Sacamoto84/ESP32_C3_Uart_to_Udp/src/network/refreshTcpClientConnectionState.cpp

#include "network_internal.h"

// Обновляет кэшированное состояние потокового клиента без опоры на короткое замыкание bool().
bool refreshTcpClientConnectionState(const char *disconnectReason)
{
    if (tcpClient.connected())
    {
        tcpClientConnected = true;
        return true;
    }

    if (tcpClientConnected)
    {
        disconnectTcpClient(disconnectReason);
    }

    return false;
}
