Sacamoto84/ESP32_C3_Uart_to_Udp/src/network/initWiFi.cpp

#include "network_internal.h"
#include "status_led.h"

namespace
{
// Загружает и проверяет сохранённые поля static IP перед запуском Wi-Fi.
bool loadStaticIpConfig(IPAddress &localIp, IPAddress &gateway, IPAddress &subnet)
{
    String localIpString = db.get(kk::staticIp);
    String gatewayString = db.get(kk::staticGateway);
    String subnetString = db.get(kk::staticSubnet);

    const bool ok = localIp.fromString(localIpString) &&
                    gateway.fromString(gatewayString) &&
                    subnet.fromString(subnetString);

    if (!ok)
    {
        projectLog.println("Static IP enabled, but one of the IP fields is invalid. Falling back to DHCP");
    }

    return ok;
}

#if PROJECT_HAS_SCREEN
#if SCREEN_WIDTH == 72 && SCREEN_HEIGHT == 40
constexpr const uint8_t *kStartupDisplayFont = u8g2_font_4x6_tf;
constexpr uint8_t kStartupSubtitleY = 8;
constexpr uint8_t kStartupProgressY = 16;
constexpr uint8_t kStartupMessageY = 24;
#else
constexpr const uint8_t *kStartupDisplayFont = u8g2_font_7x13_tr;
constexpr uint8_t kStartupSubtitleY = 12;
constexpr uint8_t kStartupProgressY = 24;
constexpr uint8_t kStartupMessageY = 36;
#endif

// Сбрасывает стартовый экран в единое текстовое состояние рисования.
void beginStartupScreenFrame()
{
    display.clearBuffer();
    display.setDrawColor(1);
    display.setFontMode(1);
    display.setFont(kStartupDisplayFont);
    display.setFontPosTop();
}

// Рисует простую индикацию прогресса в виде точек.
void drawDotProgress(uint8_t y, int count)
{
    if (count <= 0)
    {
        return;
    }

    display.setCursor(0, y);
    for (int i = 0; i < count && i < 20; ++i)
    {
        display.print('.');
    }
}

// Рисует один кадр стартового/прогресс-экрана во время подключения Wi-Fi.
void renderWiFiStartupScreen(const char *title, const char *subtitle, int dots, const char *message)
{
    beginStartupScreenFrame();

    if (title != nullptr && title[0] != '\0')
    {
        display.setCursor(0, 0);
        display.print(title);
    }

    if (subtitle != nullptr && subtitle[0] != '\0')
    {
        display.setCursor(0, kStartupSubtitleY);
        display.print(subtitle);
    }

    drawDotProgress(kStartupProgressY, dots);

    if (message != nullptr && message[0] != '\0')
    {
        display.setCursor(0, kStartupMessageY);
        display.print(message);
    }

    drawStartupVersionFooter();
    display.sendBuffer();
}
#endif
}

// Подключается к Wi-Fi по сохранённым настройкам и при необходимости уходит в AP-режим.
void initWiFi()
{
    int count = 0;
    bool needAP = false;

    // Перед стартом Wi-Fi опускаем частоту CPU, чтобы уменьшить пик потребления.
    setCpuFrequencyMhz(80);

    WiFi.mode(WIFI_STA);

    if (db.get(kk::useStaticIp))
    {
        IPAddress localIp;
        IPAddress gateway;
        IPAddress subnet;

        if (loadStaticIpConfig(localIp, gateway, subnet))
        {
            if (WiFi.config(localIp, gateway, subnet))
            {
                projectLog.print("Static IP enabled: ");
                projectLog.print(localIp);
                projectLog.print(" gateway ");
                projectLog.print(gateway);
                projectLog.print(" subnet ");
                projectLog.println(subnet);
            }
            else
            {
                projectLog.println("WiFi.config failed, falling back to DHCP");
            }
        }
    }

    // Мощность берём из настроек; позже можем понизить её до 8.5 dBm при ретрае.
    // Старые/повреждённые значения не позволяем применить выше 19.5 dBm.
    const int savedPower = db.get(kk::wifiPower);
    const int requestedPower = sanitizeConfiguredWifiTxPower(savedPower);
    if (requestedPower != savedPower)
    {
        projectLog.printf("WiFi TX power: saved value %d is unsupported, reset to %d\n",
                      savedPower,
                      requestedPower);
        db.set(kk::wifiPower, requestedPower);
        db.update();
    }

    const bool txPowerApplied = WiFi.setTxPower((wifi_power_t)requestedPower);
    const int actualPower = WiFi.getTxPower();
    projectLog.printf("WiFi TX power: saved=%d requested=%d actual=%d (%s), apply=%s\n",
                  savedPower,
                  requestedPower,
                  actualPower,
                  WifiCurrentPowerString(actualPower).c_str(),
                  txPowerApplied ? "ok" : "failed");
    WiFi.begin(db.get(kk::WIFI_SSID), db.get(kk::WIFI_PASS));
    sendStatusLedCommand(StatusLedCommand::ConnectingToStation);

#if PROJECT_HAS_SCREEN
    {
        const String powerLabel = WifiCurrentPowerString(WiFi.getTxPower());
        renderWiFiStartupScreen("Connecting", powerLabel.c_str(), 0, nullptr);
    }
#endif

    while (WiFi.status() != WL_CONNECTED)
    {
#if PROJECT_HAS_SCREEN
        {
            const String powerLabel = WifiCurrentPowerString(WiFi.getTxPower());
            renderWiFiStartupScreen("Connecting", powerLabel.c_str(), count + 1, nullptr);
        }
#endif
        projectLog.print(db.get(kk::wifiPower));
        projectLog.print(".");
        delay(500);
        count++;

        if (count <= 20)
        {
            continue;
        }

#if PROJECT_HAS_SCREEN
        renderWiFiStartupScreen("Connecting", "8.5 dBm", 0, "Retry power");
#endif
        projectLog.println("\nWifi STA not found");
        projectLog.println("Lowering power to 8.5dBm");

        WiFi.setTxPower(WIFI_POWER_8_5dBm);
        WiFi.begin(db.get(kk::WIFI_SSID), db.get(kk::WIFI_PASS));
        count = 0;

        while (WiFi.status() != WL_CONNECTED)
        {
#if PROJECT_HAS_SCREEN
            renderWiFiStartupScreen("Connecting", "8.5 dBm", count + 1, "Retry power");
#endif
            projectLog.print(".");
            delay(500);
            count++;

            if (count <= 20)
            {
                continue;
            }

            projectLog.println("Wifi STA not found");
            needAP = true;
            break;
        }

        break;
    }

    if (needAP)
    {
#if PROJECT_HAS_SCREEN
        renderWiFiStartupScreen("Starting AP", "AP ESP32", 0, nullptr);
#endif
        projectLog.println("Starting access point");
        WiFi.mode(WIFI_AP);
        WiFi.softAP("AP ESP32");
        sendStatusLedCommand(StatusLedCommand::AccessPoint);

        if (AP_MODE_PIN >= 0 && AP_MODE_PIN != STATUS_LED_BOARD_PIN)
        {
            pinMode(AP_MODE_PIN, OUTPUT);
            digitalWrite(AP_MODE_PIN, LOW);
        }
    }
    else
    {
        sendStatusLedCommand(StatusLedCommand::WaitingForClient);
    }

#if PROJECT_HAS_SCREEN
    {
        const String connectedHost = (needAP ? WiFi.softAPIP() : WiFi.localIP()).toString();
        renderWiFiStartupScreen("Connected", connectedHost.c_str(), 0, nullptr);
    }
#endif

    projectLog.println();
    projectLog.print("Connected: ");
    projectLog.println(needAP ? WiFi.softAPIP() : WiFi.localIP());
}
