Sacamoto84/ESP32_C3_Uart_to_Udp/src/settings_portal.cpp

#include "settings_portal.h"

#include "app_globals.h"
#include "display.h"
#include "hardware.h"
#include "network_bridge.h"
#include "status_led.h"

#include <esp_wifi.h>
#include <lwip/inet.h>

namespace
{
    // Полностью перестраивает интерфейс SettingsGyver для текущего запроса.
    void buildSettingsPage(sets::Builder &b);

    // Набор кнопок выбора фиксированной мощности Wi-Fi.
    struct WifiPowerOption
    {
        int dbValue;
        const char *label;
    };

    constexpr WifiPowerOption kWifiPowerOptions[] = {
        {-4, "-1dbm (-4)"},
        {8, "2dBm (8)"},
        {34, "8.5dBm (34)"},
        {44, "11dBm (44)"},
        {52, "13dBm (52)"},
        {60, "15dBm (60)"},
        {68, "17dBm (68)"},
        {76, "19dBm (76)"},
        {78, "19.5dBm (78)"},
    };

    // Рисует одну кнопку мощности Wi-Fi и сохраняет пресет для следующего старта.
    void addWifiPowerButton(sets::Builder &b, size_t id, const WifiPowerOption &option, int currentPower)
    {
        const uint32_t color = (currentPower != option.dbValue) ? 0x808080 : 0xd55f30;
        if (b.Button(id, option.label, color))
        {
            // init с int одновременно исправляет старую запись, которая могла
            // быть сохранена как enum и при чтении давать 0.
            db.init(kk::wifiPower, option.dbValue);
            db.set(kk::wifiPower, option.dbValue);
            db.update();

            projectLog.print("Saved WiFi TX power for next restart: ");
            projectLog.print(option.label);
            projectLog.print(", stored=");
            projectLog.println((int)db.get(kk::wifiPower));
            b.reload();
        }
    }

    // Проверяет IPv4-строку перед сохранением в БД настроек.
    bool isValidIp(const char *ip)
    {
        struct in_addr addr;
        return inet_aton(ip, &addr);
    }

    // Общий обработчик полей static IP с валидацией и перезагрузкой страницы.
    template <typename TKey>
    void handleIpInput(sets::Builder &b, TKey key, const char *label)
    {
        String tempValue = db.get(key);
        if (!b.Input(label, &tempValue))
        {
            return;
        }

        const char *ip = b.build.value.c_str();
        if (!isValidIp(ip))
        {
            projectLog.printf("Invalid IP for %s: %s\n", label, ip);
            sett.reload(true);
            return;
        }

        projectLog.printf("Saved %s: %s\n", label, ip);
        db.set(key, ip);
        db.update();
        sett.reload(true);
    }

    // Возвращает IP, который должен отображаться в портале для текущего Wi-Fi режима.
    IPAddress currentPortalIp()
    {
        return isAccessPointMode() ? WiFi.softAPIP() : WiFi.localIP();
    }
}

// Запускает портал настроек и привязывает обработчик построения интерфейса.
void initSettings()
{
    sett.begin(true);
    sett.onBuild(buildSettingsPage);
}

namespace
{
// Полностью перестраивает интерфейс SettingsGyver для текущего запроса.
void buildSettingsPage(sets::Builder &b)
{
    {
        sets::Group g(b, "Статус");

        const String currentIpLabel = "ESP32 IP: " + currentPortalIp().toString();
        b.Label(currentIpLabel.c_str());
        const String otaLabel = "OTA: " + String(PROJECT_DEVICE_HOSTNAME) + ".local:" + String(PROJECT_OTA_PORT);
        b.Label(otaLabel.c_str());
        b.Label(PROJECT_OTA_PASSWORD_VALUE[0] ? "OTA auth: enabled" : "OTA auth: disabled");

        b.Label("Порт TCP сервера: 8888");

        String queueLabel = "Очередь UART->TCP: " + String(getNetworkTxQueueCapacity()) +
                            " x " + String(NETWORK_TX_CHUNK_SIZE) + " байт";
        b.Label(queueLabel.c_str());

        const String ram = "psramSize=" + String(ESP.getPsramSize()) + " freePsram=" + String(ESP.getFreePsram()) + "\nmaxPsramBlock=" + String(ESP.getMaxAllocPsram()) + " freeHeap=" + String(ESP.getFreeHeap());
        b.Paragraph("", Text(ram));
    }

    {
        sets::Group g(b, "Настройка");

        b.Number(kk::Serial2Bitrate, "Битрейт", nullptr, 300, 4000000);

        if (b.Number(kk::serialRxBufferKb,
                     "RX буфер Serial, KB",
                     nullptr,
                     kSerialRxBufferMinKb,
                     kSerialRxBufferMaxKb))
        {
            db.update();
            b.reload();
        }

        if (b.Number(kk::networkTxQueueLength,
                     "Размер TX-очереди",
                     nullptr,
                     kNetworkTxQueueMinLength,
                     kNetworkTxQueueMaxLength))
        {
            db.update();
            b.reload();
        }
        b.Label("Применится после перезагрузки ESP32");

        if (getNetworkTxQueueCapacity() == 0)
        {
            b.Paragraph("", Text("Очередь не создалась, проверьте лог и уменьшите размеры буферов"));
        }
        else
        {
            b.Paragraph("", Text("При переполнении новые данные дропаются без краша прошивки"));
        }

        b.Switch(kk::echo, "Эхо");

        if (b.Switch(kk::statusLedEnabled, "LED включен"))
        {
            db.update();
            sendStatusLedCommand(StatusLedCommand::RefreshBrightness);
            b.reload();
        }

        if (b.Switch(kk::statusLedActiveLow, "LED active LOW"))
        {
            db.update();
            sendStatusLedCommand(StatusLedCommand::RefreshBrightness);
            b.reload();
        }

        if (b.Number(kk::statusLedBrightness,
                     "Яркость LED",
                     nullptr,
                     kStatusLedBrightnessMin,
                     kStatusLedBrightnessMax))
        {
            db.update();
            sendStatusLedCommand(StatusLedCommand::RefreshBrightness);
            b.reload();
        }

#if PROJECT_HAS_SCREEN
        // Яркость задаётся напрямую в диапазоне 0..255,
        // чтобы без преобразований писать значение в контроллер дисплея.
        if (b.Number(kk::screenBrightness, "Яркость экрана", nullptr, 0, 255))
        {
            const int brightness = constrain((int)db.get(kk::screenBrightness), 0, 255);
            applyDisplayBrightness((uint8_t)brightness);
            db.update();
            b.reload();
            sett.reload(true);
        }
#endif
    }

    {
        // Блок Wi-Fi настроек: SSID/пароль и опциональный static IP.
        sets::Group g(b, "WiFi");
        b.Input(kk::WIFI_SSID, "SSID");
        b.Input(kk::WIFI_PASS, "Password");
    }

    {
        sets::Group g(b, "Диагностика");
        if (b.Switch(kk::tcpEsp32LogEnabled, "Логи ESP32 в TCP 8888"))
        {
            const bool enabled = db.get(kk::tcpEsp32LogEnabled);
            setTcpEsp32LogEnabled(enabled);
            db.update();

            if (enabled)
            {
                projectLog.println("TCP ESP32 logging enabled");
            }

            b.reload();
        }
        b.Label("Формат TCP-лога", "[esp32] сообщение");
    }

     {
        sets::Group g(b, "IP");

        if (b.Switch(kk::useStaticIp, "Использовать static IP"))
        {
            sett.reload(true);
        }

        if (db.get(kk::useStaticIp))
        {
            // Для static IP нужен не только адрес ESP32,
            // но и gateway плюс маска сети.
            handleIpInput(b, kk::staticIp, "Static IP");
            handleIpInput(b, kk::staticGateway, "Gateway");
            handleIpInput(b, kk::staticSubnet, "Subnet mask");
            b.Label("Static IP применяется после перезагрузки ESP32");
        }
    }

    {
        // Отдельное меню выбора мощности Wi-Fi передатчика.
        sets::Menu m(b, "Мощность Wifi");
        b.enterMenu();
        const int currentPower = db.get(kk::wifiPower);
        b.Label("Сейчас", WifiCurrentPowerString(WiFi.getTxPower()));
        b.Label("После перезагрузки", WifiCurrentPowerString(currentPower));
        for (size_t i = 0; i < sizeof(kWifiPowerOptions) / sizeof(WifiPowerOption); ++i)
        {
            addWifiPowerButton(b, 1000 + i, kWifiPowerOptions[i], currentPower);
        }

        if (b.Button("Перезагрузка ESP32"))
        {
            ESP.restart();
        }
    }

#if PROJECT_HAS_SCREEN
    b.Switch(kk::externalScreen, "Внешний экран по UDP 82 порту");
#endif

    if (b.Button("Перезагрузка ESP32"))
    {
        ESP.restart();
    }

    // Аппаратный импульс сброса на внешнее устройство.
    if (b.Button("Выход -> Сброс", 0x25b18f))
    {
        projectLog.println("Выход -> Сброс");
        pulseResetLine();
    }

    // Полная очистка базы настроек.
    if (b.Button("Очистка базы", 0x25b18f))
    {
        projectLog.println("Очистка базы");
        db.clear();
        db.update();
    }


    b.Label("Версия " FW_VERSION);
}
}
