Sacamoto84/ESP32_C3_Uart_to_Udp/src/app_globals.cpp

#include "app_globals.h"

// Определения общих глобальных объектов, объявленных в app_globals.h.
WiFiUDP udp;
WiFiUDP heartbeatUdp;
WiFiServer tcpServer(8888);
WiFiClient tcpClient;
WiFiServer tcpCommandServer(8900);
WiFiClient tcpCommandClient;
QueueHandle_t uartQueue;
QueueHandle_t networkTxQueue;
std::atomic<bool> tcpClientConnected{false};
std::atomic<uint32_t> droppedNetworkTxBytes{0};
std::atomic<uint32_t> actualNetworkTxQueueLength{0};

// Постоянное хранилище настроек и веб-портал живут всё время работы прошивки.
GyverDBFile db(&LittleFS, "/data.db", 500);
SettingsGyver sett("My Settings", &db);

// Конкретный тип и конструктор OLED зависят от варианта платы и используемой шины.
#if PROJECT_HAS_SCREEN
#if OLED_USE_I2C
OledDisplay display(U8G2_R0, OLED_RESET_U8G2_PIN);
#else
OledDisplay display(U8G2_R0, OLED_CS_PIN, OLED_DC_PIN, OLED_RESET_U8G2_PIN);
#endif
#endif
