Sacamoto84/ESP32_C3_Uart_to_Udp/include/uart_bridge.h

#pragma once

#include "define.h"

// Настраивает UART0, выделяет буферы драйвера и запускает задачу чтения UART.
void initUART();

// Читает события UART, вытаскивает входящие байты и отправляет их в TCP-очередь.
void uartTask(void *arg);
